KSullivan20221/SimHub-BMW-E46-Cluster-Module/Arduino Code/main-simhub-code/GroupPictures/6c595 GEAR DISPLAY.jpg

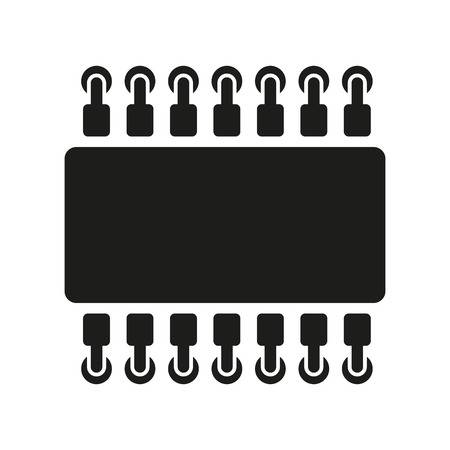
Arduino Code/main-simhub-code/GroupPictures/6c595 GEAR DISPLAY.jpg
