KSullivan20221/SimHub-BMW-E46-Cluster-Module/Arduino Code/main-simhub-code/GroupPictures/20x4 I2C LCD.JPG

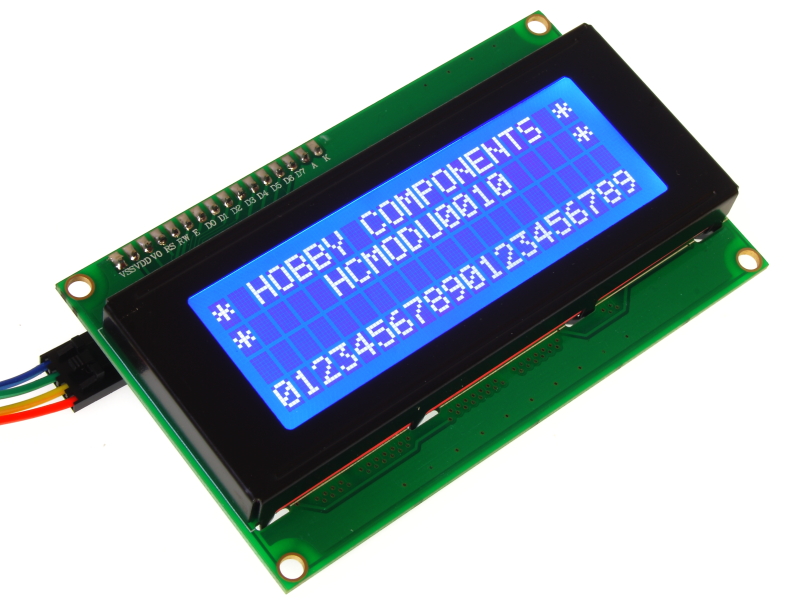
Arduino Code/main-simhub-code/GroupPictures/20x4 I2C LCD.JPG
