KSullivan20221/SimHub-BMW-E46-Cluster-Module/Arduino Code/main-simhub-code/GroupPictures/Consumption Gauge.jpg

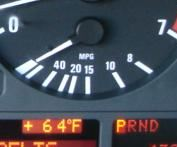
Arduino Code/main-simhub-code/GroupPictures/Consumption Gauge.jpg
