KSullivan20221/SimHub-BMW-E46-Cluster-Module/Arduino Code/main-simhub-code/GroupPictures/Gamepad analog axis.jpg

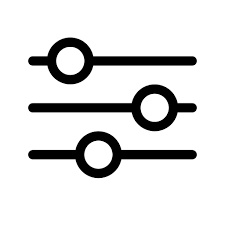
Arduino Code/main-simhub-code/GroupPictures/Gamepad analog axis.jpg
