KSullivan20221/SimHub-BMW-E46-Cluster-Module/Arduino Code/main-simhub-code/GroupPictures/GENERAL.jpg

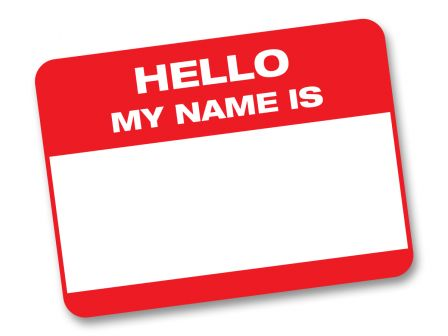
Arduino Code/main-simhub-code/GroupPictures/GENERAL.jpg
