KSullivan20221/SimHub-BMW-E46-Cluster-Module/Arduino Code/main-simhub-code/GroupPictures/HT16K33 7 Segments Module.jpg

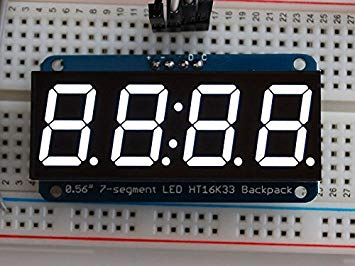
Arduino Code/main-simhub-code/GroupPictures/HT16K33 7 Segments Module.jpg
