KSullivan20221/SimHub-BMW-E46-Cluster-Module/Arduino Code/main-simhub-code/GroupPictures/PL9823 RGB Leds.jpg

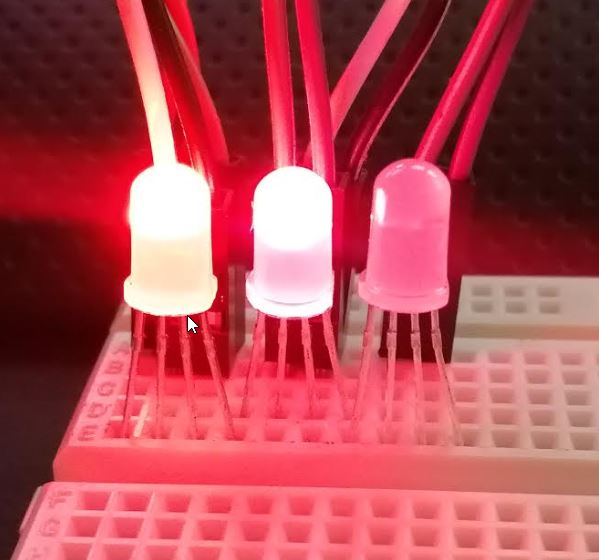
Arduino Code/main-simhub-code/GroupPictures/PL9823 RGB Leds.jpg
