KSullivan20221/SimHub-BMW-E46-Cluster-Module/Arduino Code/main-simhub-code/GroupPictures/ROTARY ENCODERS.jpg

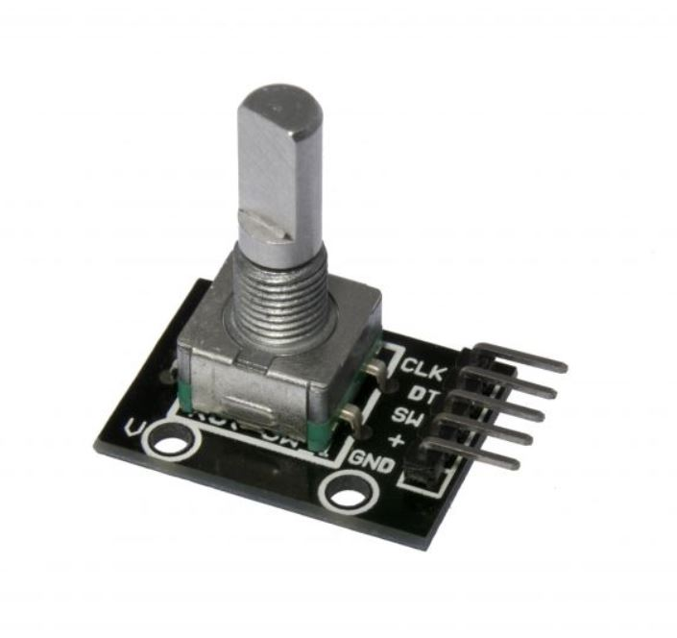
Arduino Code/main-simhub-code/GroupPictures/ROTARY ENCODERS.jpg
