KSullivan20221/SimHub-BMW-E46-Cluster-Module/Arduino Code/main-simhub-code/GroupPictures/SHAKEIT Dual VNH5019.jpg

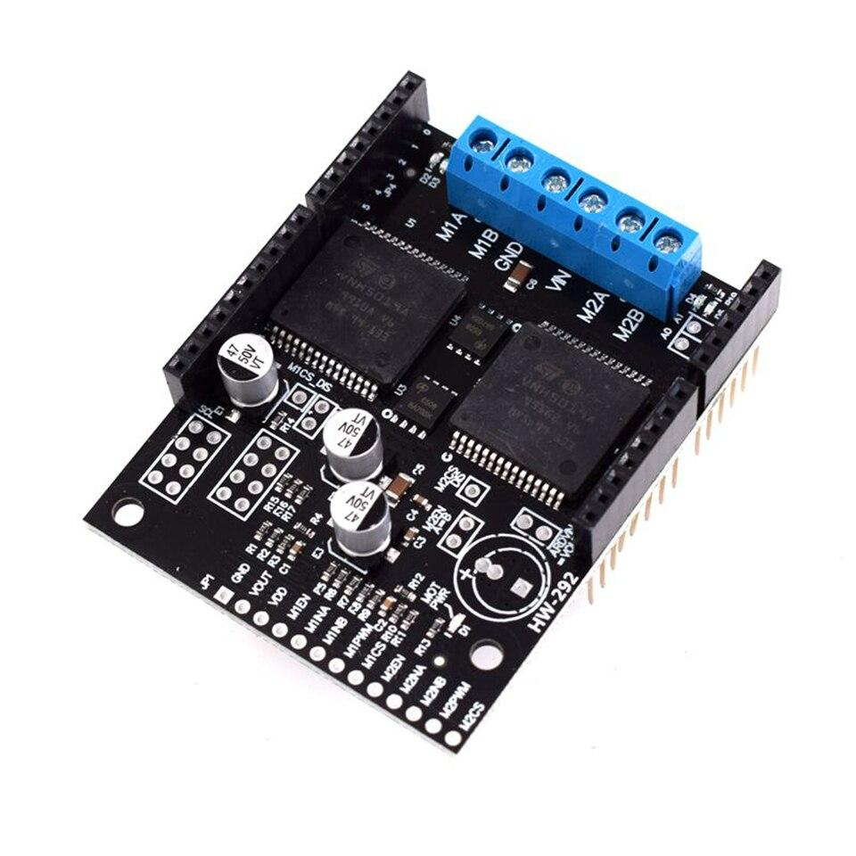
Arduino Code/main-simhub-code/GroupPictures/SHAKEIT Dual VNH5019.jpg
