KSullivan20221/SimHub-BMW-E46-Cluster-Module/Arduino Code/main-simhub-code/GroupPictures/SHAKEIT MotoMonster board.jpg

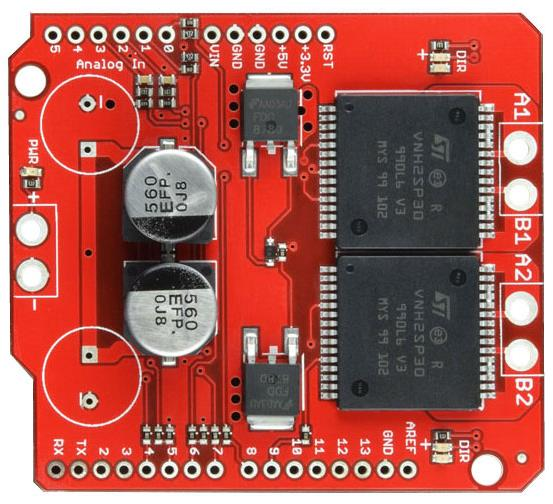
Arduino Code/main-simhub-code/GroupPictures/SHAKEIT MotoMonster board.jpg
