KSullivan20221/SimHub-BMW-E46-Cluster-Module/Arduino Code/main-simhub-code/GroupPictures/SHAKEIT PWM OUTPUTS.jpg

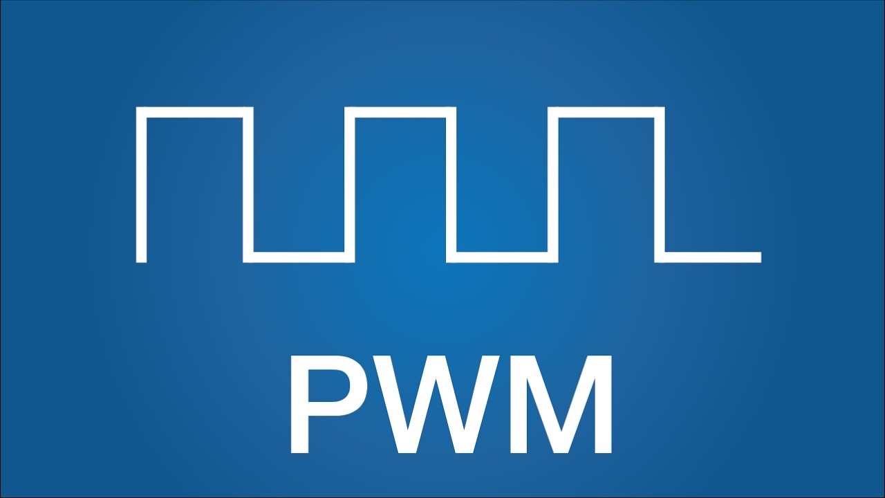
Arduino Code/main-simhub-code/GroupPictures/SHAKEIT PWM OUTPUTS.jpg
