KSullivan20221/SimHub-BMW-E46-Cluster-Module/Arduino Code/main-simhub-code/GroupPictures/TACHOMETER.jpg

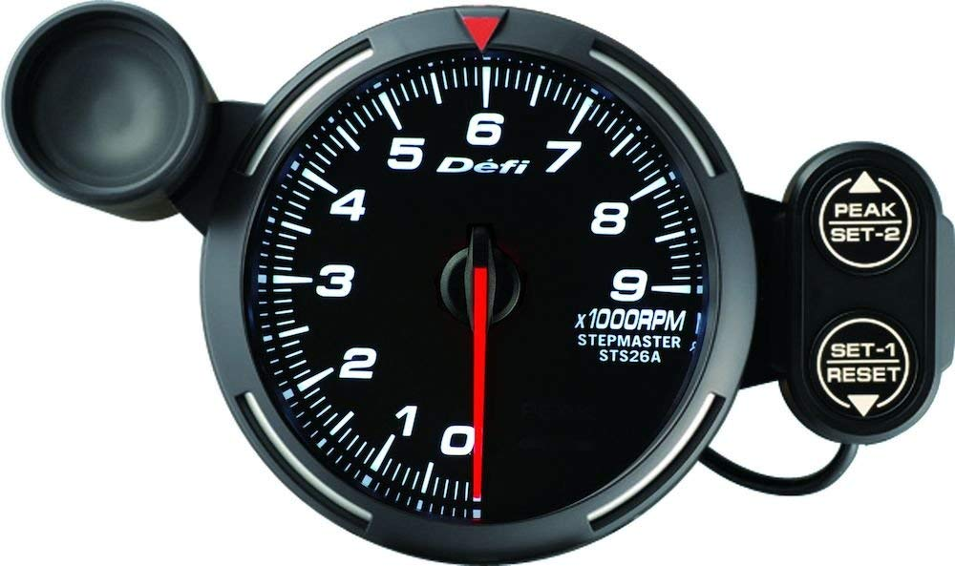
Arduino Code/main-simhub-code/GroupPictures/TACHOMETER.jpg
