KSullivan20221/SimHub-BMW-E46-Cluster-Module/Arduino Code/main-simhub-code/GroupPictures/TM1637 6Digits 7 Segment Modules.jpg

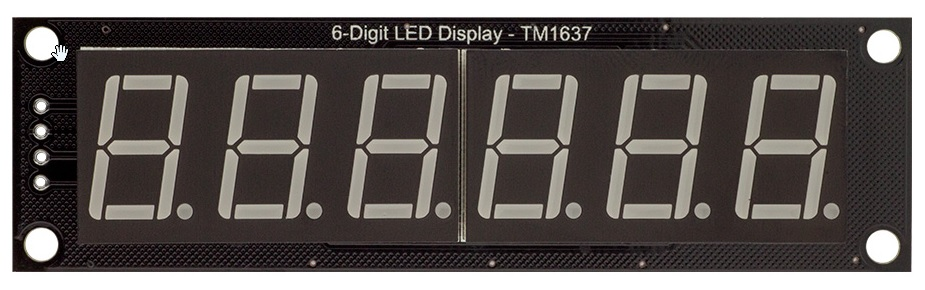
Arduino Code/main-simhub-code/GroupPictures/TM1637 6Digits 7 Segment Modules.jpg
