KSullivan20221/SimHub-BMW-E46-Cluster-Module/Arduino Code/main-simhub-code/GroupPictures/TM1638 7 Segments Modules.jpg

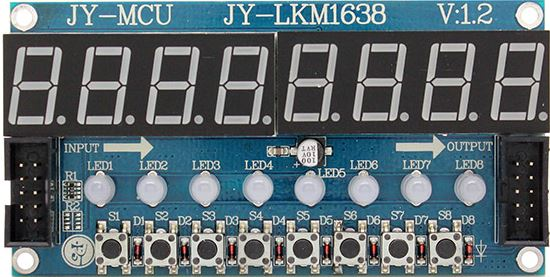
Arduino Code/main-simhub-code/GroupPictures/TM1638 7 Segments Modules.jpg
