KSullivan20221/SimHub-BMW-E46-Cluster-Module/Arduino Code/main-simhub-code/GroupPictures/WS2801 RGB Leds.jpg

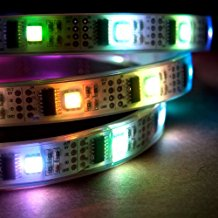
Arduino Code/main-simhub-code/GroupPictures/WS2801 RGB Leds.jpg
