KSullivan20221/SimHub-BMW-E46-Cluster-Module/Arduino Code/E46_Cluster_Test/constants.h

// Max and min speedometer values
#define MAX_SPEED 163 // MPH
#define MIN_SPEED 1 // MPH

// Max and min temperature values
#define MAX_TEMP 405 // Degrees Celcius
#define MIN_TEMP 65  // Degrees Celcius

// Max and min RPM values
#define MAX_RPM 7000
#define MIN_RPM 0
#define RPM_GAIN 6.1786
#define RPM_OFFSET 1321

// Fuel constants
#define R1_VALUE 330
#define R_POT_MAX 5000
